klaussnd/home-plant/giess-mess.sch

## KiCad design giess-mess.sch (2018-10-20, an earlier design)

Schematic: giess-mess.sch

Parts:
C1, C2, C11: 0,1µF
C3, C4, C5, C7: 100nF
C6, C8: 22pF
C9: 220pF
C10: 0,33µF
IC1: ATMEGA8-AI; TQFP32
L1, L2: 10µH
P1: VCC
P2: I2C
P3: CONN_PROG_AVR
P4: CONN_8
P5: CONN_2
P6, P7, P8, P9: CONN_4
P10: CONN_1
Q1: MOSFET_P
Q2: PNP
R1, R7: 1k
R2, R8: 1M
R3, R4: 10k
R9: 100k
R10: 2,8k
R11: 4,7k
R12: 47k
R13, R14: 20k
U1: SIM1
U2: 4011
U3: ADG728
U4: REF02
U5: TS912
U6: 78L10
U7: AD623; 1
U9: MAX333A
U10, U11: MAX339
X1: 3,6864MHz
