klaussnd/home-plant/hardware/meas-capacity.sch

## KiCad design hardware/meas-capacity.sch (2019-07-14)

Schematic: meas-capacity.sch

Parts:
C1, C4: 100n; C_0805_2012Metric
C2, C3: 22p; C_0805_2012Metric
C5, C6: 33p; C_0805_2012Metric
C7: 4.7u; C_0805_2012Metric
J2: Probe1; CONN_MINI_DIN_4
J3: Probe2; CONN_MINI_DIN_4
J4: Probe3; CONN_MINI_DIN_4
J5: Probe4; CONN_MINI_DIN_4
J6: CAN1; RJ11_RO
J7: CAN2; RJ11_RO
P1: CONN_PROG+SER_AVR; SIL-10_MYAVR+SER
Q1: BSS138; SOT-23_Handsoldering
R1: 10k; R_0805_2012Metric
R2: 10; R_0805_2012Metric
R3: 100k; R_0805_2012Metric
U1: ATMEGA168PA-AU; TQFP-32_7x7mm_P0.8mm
U2: MCP2515-E/SO; SOIC18_300
U3: MCP2551-I/SN; SOIC8_150
U4: LP2950-5.0_TO92; TO-92
Y1: 7.3728MHz; Crystal_HC49-U_Vertical
Y2: 16MHz; Crystal_HC49-U_Vertical
