klaussnd/home-plant/hardware/meas-tensio.sch

## KiCad design hardware/meas-tensio.sch (2019-07-14)

Schematic: meas-tensio.sch

Parts:
C1: 4.7u; C_0805_2012Metric
C2, C3, C4, C5, C8, C11: 100n; C_0805_2012Metric
C6, C7: 22p; C_0805_2012Metric
C9, C10: 33p; C_0805_2012Metric
C12: 10u; C_0805_2012Metric
C13: 10n; C_0805_2012Metric
J1: Tens4; CONN_MINI_DIN_4
J2: Tens3; CONN_MINI_DIN_4
J3: Tens2; CONN_MINI_DIN_4
J4: Tens1; CONN_MINI_DIN_4
J6: CAN1; RJ11_RO
J7: CAN2; RJ11_RO
JP4: ad; R_0805_2012Metric
JP5: a10; R_0805_2012Metric
L1: 10µ; L_0805_2012Metric
P1: CONN_PROG+SER_AVR; SIL-10_MYAVR+SER
Q1: BSS83P; SOT-23_Handsoldering
R1: 1k; R_0805_2012Metric
R2, R3, R5, R6, R7: 100k; R_0805_2012Metric
R8: 10; R_0805_2012Metric
R9: 10k; R_0805_2012Metric
U1: ATMEGA168PA-AU; TQFP32
U2: MCP2515-E/SO; SOIC18_300
U3: MCP2551-I/SN; SOIC8_150
U4: LP2950-5.0_TO92; TO-92
U5: AD623; DIP-8_W7.62mm
U6: TS912; SOIC8_150
U7: REF02; DIP-8_W7.62mm
U8: MAX339; SOIC16_150
Y1: 7.3728MHz; Crystal_HC49-U_Vertical
Y2: 16MHz; Crystal_HC49-U_Vertical
