klaussnd/home-plant/hardware/switch-12V.sch

## KiCad design hardware/switch-12V.sch (2019-07-14, an earlier design)

Schematic: switch-12V.sch

Parts:
C1, C4: 100n; C_0805_2012Metric
C2, C3: 22pF; C_0805_2012Metric
C5: 4.7u; C_0805_2012Metric
J1, J2: CAN; RJ11_RO
P1: CONN_PROG_AVR; SIL-10_MYAVR
P2: 12V; Molex_SPOX_5267-02A_1x02_P2.50mm_Vertical
P3, P4, P5, P6: Pump; Molex_SPOX_5267-02A_1x02_P2.50mm_Vertical
Q1, Q2, Q3, Q4: photoMOS; SOP6
R1: 10k; R_0805_2012Metric
R2, R3, R4, R5: 330; R_0805_2012Metric
U1: ATTINY24; SOIC14_150
U2: MCP2515; SOIC18_300
U3: MCP2551; SOIC8_150
U4: LP2950-5.0_TO92; TO-92
X1: 16MHz; Crystal_HC49-U_Vertical
