klaussnd/home-plant/hardware/switch-230V.sch

## KiCad design hardware/switch-230V.sch (2019-07-14)

Schematic: switch-230V.sch

Parts:
C1, C4: 100n; C_0805_2012Metric
C2, C3: 33p; C_0805_2012Metric
C5: 4.7u; C_0805_2012Metric
D1, D2, D3, D4: DIODE; D_MiniMELF
F1: FUSE; FUSE_PRINT
J1, J2: CAN; RJ11_RO
K1, K2, K3, K4: RELAY_G6D
P1: CONN_PROG_AVR; SIL-10_MYAVR
P2: 230V; PinSocket_1x01_P2.54mm_Vertical
P3, P4, P5, P6: Pump; TerminalBlock_bornier-2_P5.08mm
Q1, Q2, Q3, Q4: NPN; SOT-23
R1: 10k; R_0805_2012Metric
R2, R3, R4, R5: 15k; R_0805_2012Metric
U1: ATTINY24; SOIC14_150
U2: MCP2515; SOIC18_300
U3: MCP2551; SOIC8_150
U4: LP2950-5.0_TO92; TO-92
X1: 16MHz; Crystal_HC49-U_Vertical
